2dom/IR7_streaming_radio/Images/bad_radio.jpg

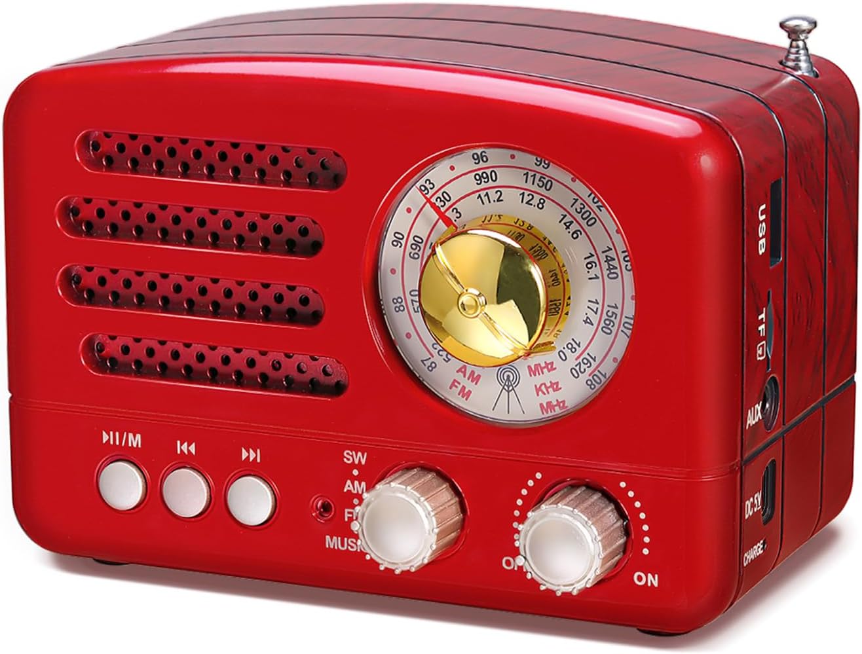
Images/bad_radio.jpg
