2dom/IR7_streaming_radio/Images/P5020376.JPG

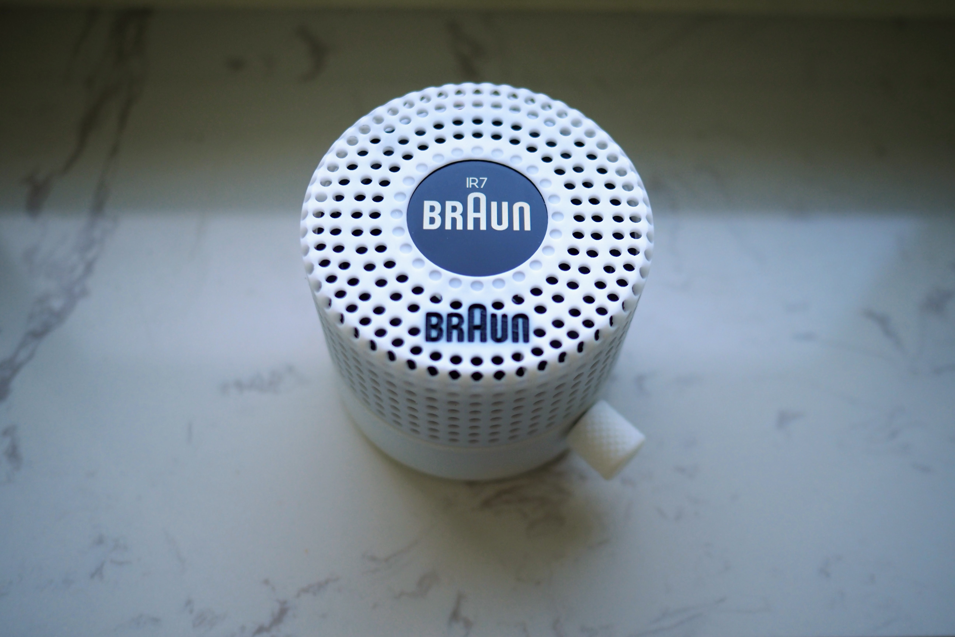
Images/P5020376.JPG
