2dom/IR7_streaming_radio/Images/P6030401.JPG

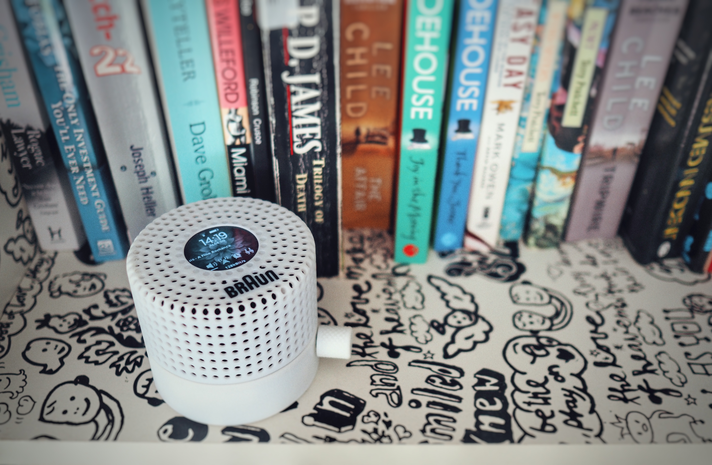
Images/P6030401.JPG
