2dom/IR7_streaming_radio/Images/PXL_20250604_143115881~2-EDIT.jpg

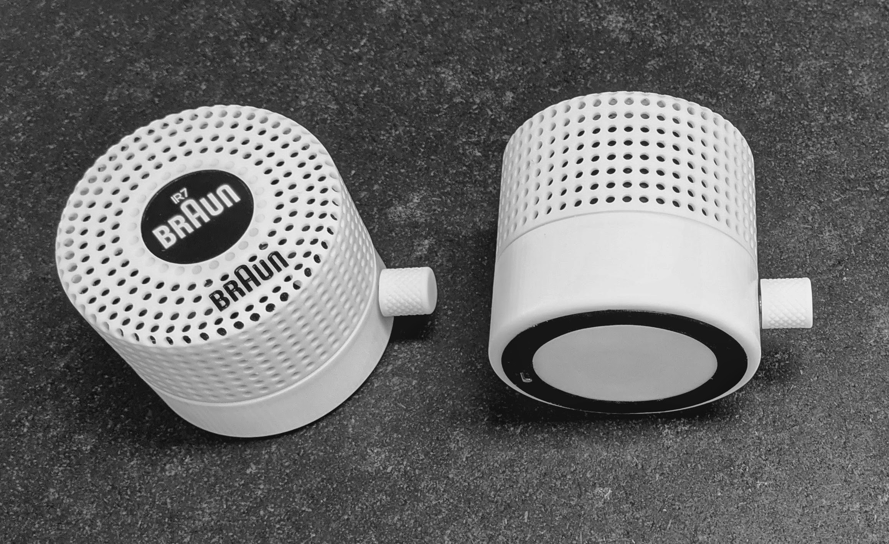
Images/PXL_20250604_143115881~2-EDIT.jpg
