2dom/IR7_streaming_radio/Images/Radio_Clock v38g~2.png

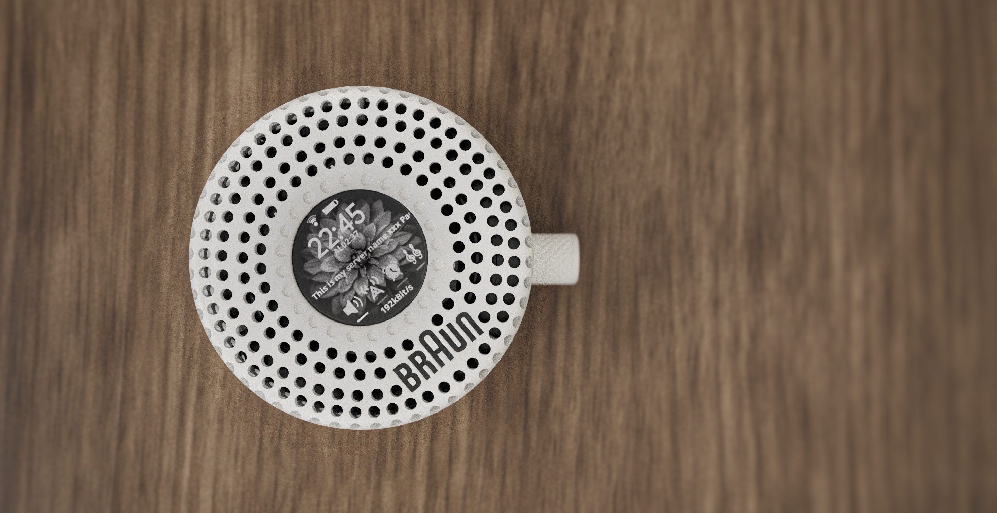
Images/Radio_Clock v38g~2.png
